Carlivats/Autonomous_Photographer/src/gallery.py

import os
from PyQt5.QtWidgets import (QWidget, QLabel, QPushButton, QVBoxLayout, 
                             QHBoxLayout, QGridLayout, QScrollArea, QFrame, QSizePolicy, QDialog)
from PyQt5.QtCore import Qt, QSize, QRect, QFileSystemWatcher, pyqtSignal
from PyQt5.QtGui import QIcon, QPixmap

from image_viewer import ImageViewer

class ImageThumbLabel(QLabel):
    """A custom label that loads an image, scales it, and center-crops it to fit a fixed box."""
    
    # Define a custom signal that emits the file path when clicked
    clicked = pyqtSignal(str) 

    def __init__(self, image_path, w, h):
        super().__init__()
        self.image_path = image_path
        
        self.setFixedSize(w, h)
        self.setStyleSheet("background-color: #2c3038; border-radius: 4px;")
        self.setAlignment(Qt.AlignCenter)
        
        # Change the cursor to a pointing hand so the user knows it's clickable
        self.setCursor(Qt.PointingHandCursor)

        # Load and crop the image
        original_pixmap = QPixmap(self.image_path)
        if not original_pixmap.isNull():
            target_size = QSize(w, h)
            scaled = original_pixmap.scaled(
                target_size, 
                Qt.KeepAspectRatioByExpanding, 
                Qt.SmoothTransformation
            )
            crop_rect = QRect(
                (scaled.width() - w) // 2,
                (scaled.height() - h) // 2,
                w, h
            )
            self.setPixmap(scaled.copy(crop_rect))

    def mousePressEvent(self, event):
        if event.button() == Qt.LeftButton:
            self.clicked.emit(self.image_path)
        super().mousePressEvent(event)

class GalleryUI(QWidget):
    # 1. Add gallery_dir=None to the parameters
    def __init__(self, parent=None, gallery_dir=None):
        super().__init__()
        self.setWindowTitle("Gallery View")
        self.resize(1024, 600)
        self.setStyleSheet("background-color: #16181d; color: white;")

        self.base_dir = os.path.dirname(__file__)
        
        # 2. Use the provided directory, or default to the local 'gallery' folder
        if gallery_dir:
            self.gallery_dir = gallery_dir
        else:
            self.gallery_dir = os.path.join(self.base_dir, 'gallery')
        
        # Ensure gallery directory exists
        os.makedirs(self.gallery_dir, exist_ok=True)

        self.trash_dir = os.path.join(self.gallery_dir, '.trash')
        os.makedirs(self.trash_dir, exist_ok=True)
        self.current_view = "home"

        self.setup_ui()
        self.load_images_to_grid()

        # Set up a watcher to automatically update UI when files are added/deleted
        self.watcher = QFileSystemWatcher([self.gallery_dir])
        self.watcher.directoryChanged.connect(self.load_images_to_grid)

    def setup_ui(self):
        main_layout = QHBoxLayout(self)
        main_layout.setContentsMargins(0, 0, 0, 0)
        main_layout.setSpacing(0)

        # ==========================================
        # LEFT SIDE: Scrollable Image Grid
        # ==========================================
        self.scroll_area = QScrollArea()
        self.scroll_area.setWidgetResizable(True)
        self.scroll_area.setStyleSheet("QScrollArea { border: none; }")
        self.scroll_area.setHorizontalScrollBarPolicy(Qt.ScrollBarAlwaysOff)

        self.gallery_container = QWidget()
        self.gallery_layout = QVBoxLayout(self.gallery_container) 
        self.gallery_layout.setSpacing(10)
        self.gallery_layout.setContentsMargins(20, 20, 20, 20)

        self.scroll_area.setWidget(self.gallery_container)
        main_layout.addWidget(self.scroll_area, stretch=3)

        # ==========================================
        # RIGHT SIDE: Sidebar Controls
        # ==========================================
        sidebar = QWidget()
        sidebar.setStyleSheet("background-color: #121418;")
        sidebar_layout = QVBoxLayout(sidebar)
        sidebar_layout.setContentsMargins(30, 40, 30, 40)
        sidebar_layout.setSpacing(15)

        
        self.logo_label = QLabel()
        self.logo_label.setAlignment(Qt.AlignCenter)
        
        logo_path = os.path.join(self.base_dir, 'assets', 'logo.png') 
        
        if os.path.exists(logo_path):
            pixmap = QPixmap(logo_path)
            # Scale it to a reasonable width (e.g., 200px) so it doesn't blow up the sidebar
            scaled_pixmap = pixmap.scaledToWidth(200, Qt.SmoothTransformation)
            self.logo_label.setPixmap(scaled_pixmap)
        else:
            # Fallback just in case the file name is wrong
            self.logo_label.setText("LOGO MISSING") 
            self.logo_label.setStyleSheet("color: red; font-weight: bold;")
            
        sidebar_layout.addWidget(self.logo_label)
        sidebar_layout.addWidget(self.create_separator_line())

        self.btn_home = self.create_sidebar_button("Home", 'home.png', is_active=True)
        self.btn_trash = self.create_sidebar_button("Trash", 'trash.png', is_active=False)
        
        self.btn_home.clicked.connect(lambda: self.switch_view("home"))
        self.btn_trash.clicked.connect(lambda: self.switch_view("trash"))
        
        sidebar_layout.addWidget(self.btn_home)
        sidebar_layout.addWidget(self.btn_trash)
        sidebar_layout.addWidget(self.create_separator_line())

        sidebar_layout.addStretch()

        self.btn_back = QPushButton(" Go Back")
        self.btn_back.setFixedHeight(50)
        self.btn_back.setStyleSheet("""
            QPushButton {
                background-color: #1c2024;
                color: white; font-size: 18px; border-radius: 8px;
            }
            QPushButton:hover { background-color: #2b3038; }
            QPushButton:pressed { background-color: #525a70; }
        """)
        
        back_icon_path = os.path.join(self.base_dir, 'assets', 'back.png')
        if os.path.exists(back_icon_path):
            self.btn_back.setIcon(QIcon(back_icon_path))
            self.btn_back.setIconSize(QSize(24, 24))
            
        self.btn_back.clicked.connect(self.close) 
        sidebar_layout.addWidget(self.btn_back)

        main_layout.addWidget(sidebar, stretch=1)

        self.btn_active_style = """
            QPushButton { background-color: #2b3038; color: white; font-size: 18px; font-weight: bold; text-align: left; padding: 12px 10px; border: none; border-radius: 6px; }
        """
        self.btn_idle_style = """
            QPushButton { background-color: transparent; color: #a0aabf; font-size: 18px; text-align: left; padding: 12px 10px; border: none; }
            QPushButton:hover { color: white; background-color: #1c2024; border-radius: 6px;}
        """

    def switch_view(self, mode):
        """Swaps the UI between the Home folder and the Trash folder."""
        self.current_view = mode
        
        # Update button visuals and set the target directory
        if mode == "home":
            self.btn_home.setStyleSheet(self.btn_active_style)
            self.btn_trash.setStyleSheet(self.btn_idle_style)
            target_dir = self.gallery_dir
        else:
            self.btn_home.setStyleSheet(self.btn_idle_style)
            self.btn_trash.setStyleSheet(self.btn_active_style)
            target_dir = self.trash_dir

        # Safely re-point the auto-refresher to the new folder
        if self.watcher.directories():
            self.watcher.removePaths(self.watcher.directories())
        self.watcher.addPath(target_dir)
        
        # Redraw the grid with the new folder
        self.load_images_to_grid()

    # --- Dynamic Grid Logic ---

    def clear_layout(self, layout):
        """Removes all widgets from the layout before a refresh."""
        while layout.count():
            item = layout.takeAt(0)
            widget = item.widget()
            if widget is not None:
                widget.deleteLater()

    def load_images_to_grid(self):
        """Packs images left-to-right, wrapping to a new row when space runs out."""
        self.clear_layout(self.gallery_layout)

        # 1. Safely determine which folder to read from based on the current tab
        target_dir = self.gallery_dir if getattr(self, 'current_view', 'home') == "home" else self.trash_dir

        TARGET_HEIGHT = 180 
        SPACING = 10
        MAX_ROW_WIDTH = 700 

        supported_formats = ('.png', '.jpg', '.jpeg', '.bmp')
        
        # 2. Get the files from the CORRECT directory
        image_files = [f for f in os.listdir(target_dir) if f.lower().endswith(supported_formats)]
        
        # 3. Sort them using the CORRECT directory path
        image_files.sort(key=lambda x: os.path.getmtime(os.path.join(target_dir, x)), reverse=True)
        
        current_row_layout = QHBoxLayout()
        current_row_layout.setSpacing(SPACING)
        current_row_width = 0

        for filename in image_files:
            # 4. Build the final file path from the CORRECT directory
            file_path = os.path.join(target_dir, filename)
            temp_pixmap = QPixmap(file_path)
            
            if temp_pixmap.isNull():
                continue
            
            is_landscape = temp_pixmap.width() >= temp_pixmap.height()
            item_width = int(TARGET_HEIGHT * (16.0 / 9.0)) if is_landscape else int(TARGET_HEIGHT * (9.0 / 16.0))

            if current_row_width + item_width > MAX_ROW_WIDTH and current_row_width > 0:
                current_row_layout.addStretch() 
                self.gallery_layout.addLayout(current_row_layout)
                current_row_layout = QHBoxLayout()
                current_row_layout.setSpacing(SPACING)
                current_row_width = 0

            thumb = ImageThumbLabel(file_path, item_width, TARGET_HEIGHT)
            thumb.clicked.connect(self.open_full_image)
            current_row_layout.addWidget(thumb)
            
            current_row_width += (item_width + SPACING)

        if current_row_width > 0:
            current_row_layout.addStretch()
            self.gallery_layout.addLayout(current_row_layout)

        self.gallery_layout.addStretch()

    # --- UI Helper Methods ---

    def open_full_image(self, image_path):
        """Spawns the modal image viewer when a thumbnail is clicked."""
        # Check the state of current_view safely, defaulting to 'home'
        is_trash = (getattr(self, 'current_view', 'home') == "trash")
        
        self.viewer = ImageViewer(image_path, is_trash=is_trash, parent=self)
        self.viewer.exec_()

    def create_separator_line(self):
        line = QFrame()
        line.setFrameShape(QFrame.HLine)
        line.setFrameShadow(QFrame.Sunken)
        line.setStyleSheet("background-color: #4a505c; max-height: 1px;")
        return line

    def create_sidebar_button(self, text, icon_filename, is_active=False):
        btn = QPushButton(f" {text}")
        icon_path = os.path.join(self.base_dir, 'assets', icon_filename)
        if os.path.exists(icon_path):
            btn.setIcon(QIcon(icon_path))
            btn.setIconSize(QSize(24, 24))
            
        if is_active:
            # Active State: Distinct background, bolder text
            btn.setStyleSheet("""
                QPushButton {
                    background-color: #2b3038; 
                    color: white; 
                    font-size: 18px;
                    font-weight: bold;
                    text-align: left; 
                    padding: 12px 10px; 
                    border: none;
                    border-radius: 6px;
                }
            """)
        else:
            # Idle State: Transparent background, fades out slightly
            btn.setStyleSheet("""
                QPushButton {
                    background-color: transparent; 
                    color: #a0aabf; 
                    font-size: 18px;
                    text-align: left; 
                    padding: 12px 10px; 
                    border: none;
                }
                QPushButton:hover { color: white; background-color: #1c2024; border-radius: 6px;}
            """)
        return btn
    
